StarNamer/dactyl-manuform-all/things/alps-holes.scad

union () {
  union () {
    union () {
      hull () {
        translate ([0, 0, 13]) {
          rotate (a=14.999999999999998, v=[0, 1, 0]) {
            translate ([0, 0, 0]) {
              translate ([0, 0, 0]) {
                translate ([0, 0, 239.07818057271746]) {
                  rotate (a=5.0, v=[0, 1, 0]) {
                    translate ([0, 0, -239.07818057271746]) {
                      translate ([0, 0, 85.26861330108649]) {
                        rotate (a=29.999999999999996, v=[1, 0, 0]) {
                          translate ([0, 0, -85.26861330108649]) {
                            translate ([-8.649999999999999, 8.649999999999999, 0]) {
                              translate ([0, 0, 2.25]) {
                                cube ([0.1, 0.1, 3.5], center=true);
                              }
                            }
                          }
                        }
                      }
                    }
                  }
                }
              }
            }
          }
        }
        translate ([0, 0, 13]) {
          rotate (a=14.999999999999998, v=[0, 1, 0]) {
            translate ([0, 0, 0]) {
              translate ([0, 0, 0]) {
                translate ([0, 0, 239.07818057271746]) {
                  rotate (a=10.0, v=[0, 1, 0]) {
                    translate ([0, 0, -239.07818057271746]) {
                      translate ([0, 0, 85.26861330108649]) {
                        rotate (a=29.999999999999996, v=[1, 0, 0]) {
                          translate ([0, 0, -85.26861330108649]) {
                            translate ([8.649999999999999, 8.649999999999999, 0]) {
                              translate ([0, 0, 2.25]) {
                                cube ([0.1, 0.1, 3.5], center=true);
                              }
                            }
                          }
                        }
                      }
                    }
                  }
                }
              }
            }
          }
        }
        translate ([0, 0, 13]) {
          rotate (a=14.999999999999998, v=[0, 1, 0]) {
            translate ([0, 0, 0]) {
              translate ([0, 0, 0]) {
                translate ([0, 0, 239.07818057271746]) {
                  rotate (a=5.0, v=[0, 1, 0]) {
                    translate ([0, 0, -239.07818057271746]) {
                      translate ([0, 0, 85.26861330108649]) {
                        rotate (a=29.999999999999996, v=[1, 0, 0]) {
                          translate ([0, 0, -85.26861330108649]) {
                            translate ([-8.649999999999999, -8.649999999999999, 0]) {
                              translate ([0, 0, 2.25]) {
                                cube ([0.1, 0.1, 3.5], center=true);
                              }
                            }
                          }
                        }
                      }
                    }
                  }
                }
              }
            }
          }
        }
      }
      hull () {
        translate ([0, 0, 13]) {
          rotate (a=14.999999999999998, v=[0, 1, 0]) {
            translate ([0, 0, 0]) {
              translate ([0, 0, 0]) {
                translate ([0, 0, 239.07818057271746]) {
                  rotate (a=10.0, v=[0, 1, 0]) {
                    translate ([0, 0, -239.07818057271746]) {
                      translate ([0, 0, 85.26861330108649]) {
                        rotate (a=29.999999999999996, v=[1, 0, 0]) {
                          translate ([0, 0, -85.26861330108649]) {
                            translate ([8.649999999999999, 8.649999999999999, 0]) {
                              translate ([0, 0, 2.25]) {
                                cube ([0.1, 0.1, 3.5], center=true);
                              }
                            }
                          }
                        }
                      }
                    }
                  }
                }
              }
            }
          }
        }
        translate ([0, 0, 13]) {
          rotate (a=14.999999999999998, v=[0, 1, 0]) {
            translate ([0, 0, 0]) {
              translate ([0, 0, 0]) {
                translate ([0, 0, 239.07818057271746]) {
                  rotate (a=5.0, v=[0, 1, 0]) {
                    translate ([0, 0, -239.07818057271746]) {
                      translate ([0, 0, 85.26861330108649]) {
                        rotate (a=29.999999999999996, v=[1, 0, 0]) {
                          translate ([0, 0, -85.26861330108649]) {
                            translate ([-8.649999999999999, -8.649999999999999, 0]) {
                              translate ([0, 0, 2.25]) {
                                cube ([0.1, 0.1, 3.5], center=true);
                              }
                            }
                          }
                        }
                      }
                    }
                  }
                }
              }
            }
          }
        }
        translate ([0, 0, 13]) {
          rotate (a=14.999999999999998, v=[0, 1, 0]) {
            translate ([0, 0, 0]) {
              translate ([0, 0, 0]) {
                translate ([0, 0, 239.07818057271746]) {
                  rotate (a=10.0, v=[0, 1, 0]) {
                    translate ([0, 0, -239.07818057271746]) {
                      translate ([0, 0, 85.26861330108649]) {
                        rotate (a=29.999999999999996, v=[1, 0, 0]) {
                          translate ([0, 0, -85.26861330108649]) {
                            translate ([8.649999999999999, -8.649999999999999, 0]) {
                              translate ([0, 0, 2.25]) {
                                cube ([0.1, 0.1, 3.5], center=true);
                              }
                            }
                          }
                        }
                      }
                    }
                  }
                }
              }
            }
          }
        }
      }
    }
    union () {
      hull () {
        translate ([0, 0, 13]) {
          rotate (a=14.999999999999998, v=[0, 1, 0]) {
            translate ([7.2, 0, 0]) {
              translate ([0, 0, 0]) {
                translate ([0, 0, 239.07818057271746]) {
                  rotate (a=5.0, v=[0, 1, 0]) {
                    translate ([0, 0, -239.07818057271746]) {
                      translate ([0, 0, 85.26861330108649]) {
                        rotate (a=14.999999999999998, v=[1, 0, 0]) {
                          translate ([0, 0, -85.26861330108649]) {
                            translate ([-8.649999999999999, 8.649999999999999, 0]) {
                              translate ([0, 0, 2.25]) {
                                cube ([0.1, 0.1, 3.5], center=true);
                              }
                            }
                          }
                        }
                      }
                    }
                  }
                }
              }
            }
          }
        }
        translate ([0, 0, 13]) {
          rotate (a=14.999999999999998, v=[0, 1, 0]) {
            translate ([7.2, 0, 0]) {
              translate ([0, 0, 0]) {
                translate ([0, 0, 239.07818057271746]) {
                  rotate (a=10.0, v=[0, 1, 0]) {
                    translate ([0, 0, -239.07818057271746]) {
                      translate ([0, 0, 85.26861330108649]) {
                        rotate (a=14.999999999999998, v=[1, 0, 0]) {
                          translate ([0, 0, -85.26861330108649]) {
                            translate ([8.649999999999999, 8.649999999999999, 0]) {
                              translate ([0, 0, 2.25]) {
                                cube ([0.1, 0.1, 3.5], center=true);
                              }
                            }
                          }
                        }
                      }
                    }
                  }
                }
              }
            }
          }
        }
        translate ([0, 0, 13]) {
          rotate (a=14.999999999999998, v=[0, 1, 0]) {
            translate ([7.2, 0, 0]) {
              translate ([0, 0, 0]) {
                translate ([0, 0, 239.07818057271746]) {
                  rotate (a=5.0, v=[0, 1, 0]) {
                    translate ([0, 0, -239.07818057271746]) {
                      translate ([0, 0, 85.26861330108649]) {
                        rotate (a=14.999999999999998, v=[1, 0, 0]) {
                          translate ([0, 0, -85.26861330108649]) {
                            translate ([-8.649999999999999, -8.649999999999999, 0]) {
                              translate ([0, 0, 2.25]) {
                                cube ([0.1, 0.1, 3.5], center=true);
                              }
                            }
                          }
                        }
                      }
                    }
                  }
                }
              }
            }
          }
        }
      }
      hull () {
        translate ([0, 0, 13]) {
          rotate (a=14.999999999999998, v=[0, 1, 0]) {
            translate ([7.2, 0, 0]) {
              translate ([0, 0, 0]) {
                translate ([0, 0, 239.07818057271746]) {
                  rotate (a=10.0, v=[0, 1, 0]) {
                    translate ([0, 0, -239.07818057271746]) {
                      translate ([0, 0, 85.26861330108649]) {
                        rotate (a=14.999999999999998, v=[1, 0, 0]) {
                          translate ([0, 0, -85.26861330108649]) {
                            translate ([8.649999999999999, 8.649999999999999, 0]) {
                              translate ([0, 0, 2.25]) {
                                cube ([0.1, 0.1, 3.5], center=true);
                              }
                            }
                          }
                        }
                      }
                    }
                  }
                }
              }
            }
          }
        }
        translate ([0, 0, 13]) {
          rotate (a=14.999999999999998, v=[0, 1, 0]) {
            translate ([7.2, 0, 0]) {
              translate ([0, 0, 0]) {
                translate ([0, 0, 239.07818057271746]) {
                  rotate (a=5.0, v=[0, 1, 0]) {
                    translate ([0, 0, -239.07818057271746]) {
                      translate ([0, 0, 85.26861330108649]) {
                        rotate (a=14.999999999999998, v=[1, 0, 0]) {
                          translate ([0, 0, -85.26861330108649]) {
                            translate ([-8.649999999999999, -8.649999999999999, 0]) {
                              translate ([0, 0, 2.25]) {
                                cube ([0.1, 0.1, 3.5], center=true);
                              }
                            }
                          }
                        }
                      }
                    }
                  }
                }
              }
            }
          }
        }
        translate ([0, 0, 13]) {
          rotate (a=14.999999999999998, v=[0, 1, 0]) {
            translate ([7.2, 0, 0]) {
              translate ([0, 0, 0]) {
                translate ([0, 0, 239.07818057271746]) {
                  rotate (a=10.0, v=[0, 1, 0]) {
                    translate ([0, 0, -239.07818057271746]) {
                      translate ([0, 0, 85.26861330108649]) {
                        rotate (a=14.999999999999998, v=[1, 0, 0]) {
                          translate ([0, 0, -85.26861330108649]) {
                            translate ([8.649999999999999, -8.649999999999999, 0]) {
                              translate ([0, 0, 2.25]) {
                                cube ([0.1, 0.1, 3.5], center=true);
                              }
                            }
                          }
                        }
                      }
                    }
                  }
                }
              }
            }
          }
        }
      }
    }
    union () {
      hull () {
        translate ([0, 0, 13]) {
          rotate (a=14.999999999999998, v=[0, 1, 0]) {
            translate ([14.4, 0, 0]) {
              translate ([0, 0, 0]) {
                translate ([0, 0, 239.07818057271746]) {
                  rotate (a=5.0, v=[0, 1, 0]) {
                    translate ([0, 0, -239.07818057271746]) {
                      translate ([0, 0, 85.26861330108649]) {
                        rotate (a=0.0, v=[1, 0, 0]) {
                          translate ([0, 0, -85.26861330108649]) {
                            translate ([-8.649999999999999, 8.649999999999999, 0]) {
                              translate ([0, 0, 2.25]) {
                                cube ([0.1, 0.1, 3.5], center=true);
                              }
                            }
                          }
                        }
                      }
                    }
                  }
                }
              }
            }
          }
        }
        translate ([0, 0, 13]) {
          rotate (a=14.999999999999998, v=[0, 1, 0]) {
            translate ([14.4, 0, 0]) {
              translate ([0, 0, 0]) {
                translate ([0, 0, 239.07818057271746]) {
                  rotate (a=10.0, v=[0, 1, 0]) {
                    translate ([0, 0, -239.07818057271746]) {
                      translate ([0, 0, 85.26861330108649]) {
                        rotate (a=0.0, v=[1, 0, 0]) {
                          translate ([0, 0, -85.26861330108649]) {
                            translate ([8.649999999999999, 8.649999999999999, 0]) {
                              translate ([0, 0, 2.25]) {
                                cube ([0.1, 0.1, 3.5], center=true);
                              }
                            }
                          }
                        }
                      }
                    }
                  }
                }
              }
            }
          }
        }
        translate ([0, 0, 13]) {
          rotate (a=14.999999999999998, v=[0, 1, 0]) {
            translate ([14.4, 0, 0]) {
              translate ([0, 0, 0]) {
                translate ([0, 0, 239.07818057271746]) {
                  rotate (a=5.0, v=[0, 1, 0]) {
                    translate ([0, 0, -239.07818057271746]) {
                      translate ([0, 0, 85.26861330108649]) {
                        rotate (a=0.0, v=[1, 0, 0]) {
                          translate ([0, 0, -85.26861330108649]) {
                            translate ([-8.649999999999999, -8.649999999999999, 0]) {
                              translate ([0, 0, 2.25]) {
                                cube ([0.1, 0.1, 3.5], center=true);
                              }
                            }
                          }
                        }
                      }
                    }
                  }
                }
              }
            }
          }
        }
      }
      hull () {
        translate ([0, 0, 13]) {
          rotate (a=14.999999999999998, v=[0, 1, 0]) {
            translate ([14.4, 0, 0]) {
              translate ([0, 0, 0]) {
                translate ([0, 0, 239.07818057271746]) {
                  rotate (a=10.0, v=[0, 1, 0]) {
                    translate ([0, 0, -239.07818057271746]) {
                      translate ([0, 0, 85.26861330108649]) {
                        rotate (a=0.0, v=[1, 0, 0]) {
                          translate ([0, 0, -85.26861330108649]) {
                            translate ([8.649999999999999, 8.649999999999999, 0]) {
                              translate ([0, 0, 2.25]) {
                                cube ([0.1, 0.1, 3.5], center=true);
                              }
                            }
                          }
                        }
                      }
                    }
                  }
                }
              }
            }
          }
        }
        translate ([0, 0, 13]) {
          rotate (a=14.999999999999998, v=[0, 1, 0]) {
            translate ([14.4, 0, 0]) {
              translate ([0, 0, 0]) {
                translate ([0, 0, 239.07818057271746]) {
                  rotate (a=5.0, v=[0, 1, 0]) {
                    translate ([0, 0, -239.07818057271746]) {
                      translate ([0, 0, 85.26861330108649]) {
                        rotate (a=0.0, v=[1, 0, 0]) {
                          translate ([0, 0, -85.26861330108649]) {
                            translate ([-8.649999999999999, -8.649999999999999, 0]) {
                              translate ([0, 0, 2.25]) {
                                cube ([0.1, 0.1, 3.5], center=true);
                              }
                            }
                          }
                        }
                      }
                    }
                  }
                }
              }
            }
          }
        }
        translate ([0, 0, 13]) {
          rotate (a=14.999999999999998, v=[0, 1, 0]) {
            translate ([14.4, 0, 0]) {
              translate ([0, 0, 0]) {
                translate ([0, 0, 239.07818057271746]) {
                  rotate (a=10.0, v=[0, 1, 0]) {
                    translate ([0, 0, -239.07818057271746]) {
                      translate ([0, 0, 85.26861330108649]) {
                        rotate (a=0.0, v=[1, 0, 0]) {
                          translate ([0, 0, -85.26861330108649]) {
                            translate ([8.649999999999999, -8.649999999999999, 0]) {
                              translate ([0, 0, 2.25]) {
                                cube ([0.1, 0.1, 3.5], center=true);
                              }
                            }
                          }
                        }
                      }
                    }
                  }
                }
              }
            }
          }
        }
      }
    }
    union () {
      hull () {
        translate ([0, 0, 13]) {
          rotate (a=14.999999999999998, v=[0, 1, 0]) {
            translate ([21.6, 0, 0]) {
              translate ([0, 0, 0]) {
                translate ([0, 0, 239.07818057271746]) {
                  rotate (a=5.0, v=[0, 1, 0]) {
                    translate ([0, 0, -239.07818057271746]) {
                      translate ([0, 0, 85.26861330108649]) {
                        rotate (a=-14.999999999999998, v=[1, 0, 0]) {
                          translate ([0, 0, -85.26861330108649]) {
                            translate ([-8.649999999999999, 8.649999999999999, 0]) {
                              translate ([0, 0, 2.25]) {
                                cube ([0.1, 0.1, 3.5], center=true);
                              }
                            }
                          }
                        }
                      }
                    }
                  }
                }
              }
            }
          }
        }
        translate ([0, 0, 13]) {
          rotate (a=14.999999999999998, v=[0, 1, 0]) {
            translate ([21.6, 0, 0]) {
              translate ([0, 0, 0]) {
                translate ([0, 0, 239.07818057271746]) {
                  rotate (a=10.0, v=[0, 1, 0]) {
                    translate ([0, 0, -239.07818057271746]) {
                      translate ([0, 0, 85.26861330108649]) {
                        rotate (a=-14.999999999999998, v=[1, 0, 0]) {
                          translate ([0, 0, -85.26861330108649]) {
                            translate ([8.649999999999999, 8.649999999999999, 0]) {
                              translate ([0, 0, 2.25]) {
                                cube ([0.1, 0.1, 3.5], center=true);
                              }
                            }
                          }
                        }
                      }
                    }
                  }
                }
              }
            }
          }
        }
        translate ([0, 0, 13]) {
          rotate (a=14.999999999999998, v=[0, 1, 0]) {
            translate ([21.6, 0, 0]) {
              translate ([0, 0, 0]) {
                translate ([0, 0, 239.07818057271746]) {
                  rotate (a=5.0, v=[0, 1, 0]) {
                    translate ([0, 0, -239.07818057271746]) {
                      translate ([0, 0, 85.26861330108649]) {
                        rotate (a=-14.999999999999998, v=[1, 0, 0]) {
                          translate ([0, 0, -85.26861330108649]) {
                            translate ([-8.649999999999999, -8.649999999999999, 0]) {
                              translate ([0, 0, 2.25]) {
                                cube ([0.1, 0.1, 3.5], center=true);
                              }
                            }
                          }
                        }
                      }
                    }
                  }
                }
              }
            }
          }
        }
      }
      hull () {
        translate ([0, 0, 13]) {
          rotate (a=14.999999999999998, v=[0, 1, 0]) {
            translate ([21.6, 0, 0]) {
              translate ([0, 0, 0]) {
                translate ([0, 0, 239.07818057271746]) {
                  rotate (a=10.0, v=[0, 1, 0]) {
                    translate ([0, 0, -239.07818057271746]) {
                      translate ([0, 0, 85.26861330108649]) {
                        rotate (a=-14.999999999999998, v=[1, 0, 0]) {
                          translate ([0, 0, -85.26861330108649]) {
                            translate ([8.649999999999999, 8.649999999999999, 0]) {
                              translate ([0, 0, 2.25]) {
                                cube ([0.1, 0.1, 3.5], center=true);
                              }
                            }
                          }
                        }
                      }
                    }
                  }
                }
              }
            }
          }
        }
        translate ([0, 0, 13]) {
          rotate (a=14.999999999999998, v=[0, 1, 0]) {
            translate ([21.6, 0, 0]) {
              translate ([0, 0, 0]) {
                translate ([0, 0, 239.07818057271746]) {
                  rotate (a=5.0, v=[0, 1, 0]) {
                    translate ([0, 0, -239.07818057271746]) {
                      translate ([0, 0, 85.26861330108649]) {
                        rotate (a=-14.999999999999998, v=[1, 0, 0]) {
                          translate ([0, 0, -85.26861330108649]) {
                            translate ([-8.649999999999999, -8.649999999999999, 0]) {
                              translate ([0, 0, 2.25]) {
                                cube ([0.1, 0.1, 3.5], center=true);
                              }
                            }
                          }
                        }
                      }
                    }
                  }
                }
              }
            }
          }
        }
        translate ([0, 0, 13]) {
          rotate (a=14.999999999999998, v=[0, 1, 0]) {
            translate ([21.6, 0, 0]) {
              translate ([0, 0, 0]) {
                translate ([0, 0, 239.07818057271746]) {
                  rotate (a=10.0, v=[0, 1, 0]) {
                    translate ([0, 0, -239.07818057271746]) {
                      translate ([0, 0, 85.26861330108649]) {
                        rotate (a=-14.999999999999998, v=[1, 0, 0]) {
                          translate ([0, 0, -85.26861330108649]) {
                            translate ([8.649999999999999, -8.649999999999999, 0]) {
                              translate ([0, 0, 2.25]) {
                                cube ([0.1, 0.1, 3.5], center=true);
                              }
                            }
                          }
                        }
                      }
                    }
                  }
                }
              }
            }
          }
        }
      }
    }
    union () {
      hull () {
        translate ([0, 0, 13]) {
          rotate (a=14.999999999999998, v=[0, 1, 0]) {
            translate ([0, 0, 0]) {
              translate ([0, 2.82, -3.0]) {
                translate ([0, 0, 239.07818057271746]) {
                  rotate (a=0.0, v=[0, 1, 0]) {
                    translate ([0, 0, -239.07818057271746]) {
                      translate ([0, 0, 85.26861330108649]) {
                        rotate (a=29.999999999999996, v=[1, 0, 0]) {
                          translate ([0, 0, -85.26861330108649]) {
                            translate ([-8.649999999999999, 8.649999999999999, 0]) {
                              translate ([0, 0, 2.25]) {
                                cube ([0.1, 0.1, 3.5], center=true);
                              }
                            }
                          }
                        }
                      }
                    }
                  }
                }
              }
            }
          }
        }
        translate ([0, 0, 13]) {
          rotate (a=14.999999999999998, v=[0, 1, 0]) {
            translate ([0, 0, 0]) {
              translate ([0, 0, 0]) {
                translate ([0, 0, 239.07818057271746]) {
                  rotate (a=5.0, v=[0, 1, 0]) {
                    translate ([0, 0, -239.07818057271746]) {
                      translate ([0, 0, 85.26861330108649]) {
                        rotate (a=29.999999999999996, v=[1, 0, 0]) {
                          translate ([0, 0, -85.26861330108649]) {
                            translate ([8.649999999999999, 8.649999999999999, 0]) {
                              translate ([0, 0, 2.25]) {
                                cube ([0.1, 0.1, 3.5], center=true);
                              }
                            }
                          }
                        }
                      }
                    }
                  }
                }
              }
            }
          }
        }
        translate ([0, 0, 13]) {
          rotate (a=14.999999999999998, v=[0, 1, 0]) {
            translate ([0, 0, 0]) {
              translate ([0, 2.82, -3.0]) {
                translate ([0, 0, 239.07818057271746]) {
                  rotate (a=0.0, v=[0, 1, 0]) {
                    translate ([0, 0, -239.07818057271746]) {
                      translate ([0, 0, 85.26861330108649]) {
                        rotate (a=29.999999999999996, v=[1, 0, 0]) {
                          translate ([0, 0, -85.26861330108649]) {
                            translate ([-8.649999999999999, -8.649999999999999, 0]) {
                              translate ([0, 0, 2.25]) {
                                cube ([0.1, 0.1, 3.5], center=true);
                              }
                            }
                          }
                        }
                      }
                    }
                  }
                }
              }
            }
          }
        }
      }
      hull () {
        translate ([0, 0, 13]) {
          rotate (a=14.999999999999998, v=[0, 1, 0]) {
            translate ([0, 0, 0]) {
              translate ([0, 0, 0]) {
                translate ([0, 0, 239.07818057271746]) {
                  rotate (a=5.0, v=[0, 1, 0]) {
                    translate ([0, 0, -239.07818057271746]) {
                      translate ([0, 0, 85.26861330108649]) {
                        rotate (a=29.999999999999996, v=[1, 0, 0]) {
                          translate ([0, 0, -85.26861330108649]) {
                            translate ([8.649999999999999, 8.649999999999999, 0]) {
                              translate ([0, 0, 2.25]) {
                                cube ([0.1, 0.1, 3.5], center=true);
                              }
                            }
                          }
                        }
                      }
                    }
                  }
                }
              }
            }
          }
        }
        translate ([0, 0, 13]) {
          rotate (a=14.999999999999998, v=[0, 1, 0]) {
            translate ([0, 0, 0]) {
              translate ([0, 2.82, -3.0]) {
                translate ([0, 0, 239.07818057271746]) {
                  rotate (a=0.0, v=[0, 1, 0]) {
                    translate ([0, 0, -239.07818057271746]) {
                      translate ([0, 0, 85.26861330108649]) {
                        rotate (a=29.999999999999996, v=[1, 0, 0]) {
                          translate ([0, 0, -85.26861330108649]) {
                            translate ([-8.649999999999999, -8.649999999999999, 0]) {
                              translate ([0, 0, 2.25]) {
                                cube ([0.1, 0.1, 3.5], center=true);
                              }
                            }
                          }
                        }
                      }
                    }
                  }
                }
              }
            }
          }
        }
        translate ([0, 0, 13]) {
          rotate (a=14.999999999999998, v=[0, 1, 0]) {
            translate ([0, 0, 0]) {
              translate ([0, 0, 0]) {
                translate ([0, 0, 239.07818057271746]) {
                  rotate (a=5.0, v=[0, 1, 0]) {
                    translate ([0, 0, -239.07818057271746]) {
                      translate ([0, 0, 85.26861330108649]) {
                        rotate (a=29.999999999999996, v=[1, 0, 0]) {
                          translate ([0, 0, -85.26861330108649]) {
                            translate ([8.649999999999999, -8.649999999999999, 0]) {
                              translate ([0, 0, 2.25]) {
                                cube ([0.1, 0.1, 3.5], center=true);
                              }
                            }
                          }
                        }
                      }
                    }
                  }
                }
              }
            }
          }
        }
      }
    }
    union () {
      hull () {
        translate ([0, 0, 13]) {
          rotate (a=14.999999999999998, v=[0, 1, 0]) {
            translate ([7.2, 0, 0]) {
              translate ([0, 2.82, -3.0]) {
                translate ([0, 0, 239.07818057271746]) {
                  rotate (a=0.0, v=[0, 1, 0]) {
                    translate ([0, 0, -239.07818057271746]) {
                      translate ([0, 0, 85.26861330108649]) {
                        rotate (a=14.999999999999998, v=[1, 0, 0]) {
                          translate ([0, 0, -85.26861330108649]) {
                            translate ([-8.649999999999999, 8.649999999999999, 0]) {
                              translate ([0, 0, 2.25]) {
                                cube ([0.1, 0.1, 3.5], center=true);
                              }
                            }
                          }
                        }
                      }
                    }
                  }
                }
              }
            }
          }
        }
        translate ([0, 0, 13]) {
          rotate (a=14.999999999999998, v=[0, 1, 0]) {
            translate ([7.2, 0, 0]) {
              translate ([0, 0, 0]) {
                translate ([0, 0, 239.07818057271746]) {
                  rotate (a=5.0, v=[0, 1, 0]) {
                    translate ([0, 0, -239.07818057271746]) {
                      translate ([0, 0, 85.26861330108649]) {
                        rotate (a=14.999999999999998, v=[1, 0, 0]) {
                          translate ([0, 0, -85.26861330108649]) {
                            translate ([8.649999999999999, 8.649999999999999, 0]) {
                              translate ([0, 0, 2.25]) {
                                cube ([0.1, 0.1, 3.5], center=true);
                              }
                            }
                          }
                        }
                      }
                    }
                  }
                }
              }
            }
          }
        }
        translate ([0, 0, 13]) {
          rotate (a=14.999999999999998, v=[0, 1, 0]) {
            translate ([7.2, 0, 0]) {
              translate ([0, 2.82, -3.0]) {
                translate ([0, 0, 239.07818057271746]) {
                  rotate (a=0.0, v=[0, 1, 0]) {
                    translate ([0, 0, -239.07818057271746]) {
                      translate ([0, 0, 85.26861330108649]) {
                        rotate (a=14.999999999999998, v=[1, 0, 0]) {
                          translate ([0, 0, -85.26861330108649]) {
                            translate ([-8.649999999999999, -8.649999999999999, 0]) {
                              translate ([0, 0, 2.25]) {
                                cube ([0.1, 0.1, 3.5], center=true);
                              }
                            }
                          }
                        }
                      }
                    }
                  }
                }
              }
            }
          }
        }
      }
      hull () {
        translate ([0, 0, 13]) {
          rotate (a=14.999999999999998, v=[0, 1, 0]) {
            translate ([7.2, 0, 0]) {
              translate ([0, 0, 0]) {
                translate ([0, 0, 239.07818057271746]) {
                  rotate (a=5.0, v=[0, 1, 0]) {
                    translate ([0, 0, -239.07818057271746]) {
                      translate ([0, 0, 85.26861330108649]) {
                        rotate (a=14.999999999999998, v=[1, 0, 0]) {
                          translate ([0, 0, -85.26861330108649]) {
                            translate ([8.649999999999999, 8.649999999999999, 0]) {
                              translate ([0, 0, 2.25]) {
                                cube ([0.1, 0.1, 3.5], center=true);
                              }
                            }
                          }
                        }
                      }
                    }
                  }
                }
              }
            }
          }
        }
        translate ([0, 0, 13]) {
          rotate (a=14.999999999999998, v=[0, 1, 0]) {
            translate ([7.2, 0, 0]) {
              translate ([0, 2.82, -3.0]) {
                translate ([0, 0, 239.07818057271746]) {
                  rotate (a=0.0, v=[0, 1, 0]) {
                    translate ([0, 0, -239.07818057271746]) {
                      translate ([0, 0, 85.26861330108649]) {
                        rotate (a=14.999999999999998, v=[1, 0, 0]) {
                          translate ([0, 0, -85.26861330108649]) {
                            translate ([-8.649999999999999, -8.649999999999999, 0]) {
                              translate ([0, 0, 2.25]) {
                                cube ([0.1, 0.1, 3.5], center=true);
                              }
                            }
                          }
                        }
                      }
                    }
                  }
                }
              }
            }
          }
        }
        translate ([0, 0, 13]) {
          rotate (a=14.999999999999998, v=[0, 1, 0]) {
            translate ([7.2, 0, 0]) {
              translate ([0, 0, 0]) {
                translate ([0, 0, 239.07818057271746]) {
                  rotate (a=5.0, v=[0, 1, 0]) {
                    translate ([0, 0, -239.07818057271746]) {
                      translate ([0, 0, 85.26861330108649]) {
                        rotate (a=14.999999999999998, v=[1, 0, 0]) {
                          translate ([0, 0, -85.26861330108649]) {
                            translate ([8.649999999999999, -8.649999999999999, 0]) {
                              translate ([0, 0, 2.25]) {
                                cube ([0.1, 0.1, 3.5], center=true);
                              }
                            }
                          }
                        }
                      }
                    }
                  }
                }
              }
            }
          }
        }
      }
    }
    union () {
      hull () {
        translate ([0, 0, 13]) {
          rotate (a=14.999999999999998, v=[0, 1, 0]) {
            translate ([14.4, 0, 0]) {
              translate ([0, 2.82, -3.0]) {
                translate ([0, 0, 239.07818057271746]) {
                  rotate (a=0.0, v=[0, 1, 0]) {
                    translate ([0, 0, -239.07818057271746]) {
                      translate ([0, 0, 85.26861330108649]) {
                        rotate (a=0.0, v=[1, 0, 0]) {
                          translate ([0, 0, -85.26861330108649]) {
                            translate ([-8.649999999999999, 8.649999999999999, 0]) {
                              translate ([0, 0, 2.25]) {
                                cube ([0.1, 0.1, 3.5], center=true);
                              }
                            }
                          }
                        }
                      }
                    }
                  }
                }
              }
            }
          }
        }
        translate ([0, 0, 13]) {
          rotate (a=14.999999999999998, v=[0, 1, 0]) {
            translate ([14.4, 0, 0]) {
              translate ([0, 0, 0]) {
                translate ([0, 0, 239.07818057271746]) {
                  rotate (a=5.0, v=[0, 1, 0]) {
                    translate ([0, 0, -239.07818057271746]) {
                      translate ([0, 0, 85.26861330108649]) {
                        rotate (a=0.0, v=[1, 0, 0]) {
                          translate ([0, 0, -85.26861330108649]) {
                            translate ([8.649999999999999, 8.649999999999999, 0]) {
                              translate ([0, 0, 2.25]) {
                                cube ([0.1, 0.1, 3.5], center=true);
                              }
                            }
                          }
                        }
                      }
                    }
                  }
                }
              }
            }
          }
        }
        translate ([0, 0, 13]) {
          rotate (a=14.999999999999998, v=[0, 1, 0]) {
            translate ([14.4, 0, 0]) {
              translate ([0, 2.82, -3.0]) {
                translate ([0, 0, 239.07818057271746]) {
                  rotate (a=0.0, v=[0, 1, 0]) {
                    translate ([0, 0, -239.07818057271746]) {
                      translate ([0, 0, 85.26861330108649]) {
                        rotate (a=0.0, v=[1, 0, 0]) {
                          translate ([0, 0, -85.26861330108649]) {
                            translate ([-8.649999999999999, -8.649999999999999, 0]) {
                              translate ([0, 0, 2.25]) {
                                cube ([0.1, 0.1, 3.5], center=true);
                              }
                            }
                          }
                        }
                      }
                    }
                  }
                }
              }
            }
          }
        }
      }
      hull () {
        translate ([0, 0, 13]) {
          rotate (a=14.999999999999998, v=[0, 1, 0]) {
            translate ([14.4, 0, 0]) {
              translate ([0, 0, 0]) {
                translate ([0, 0, 239.07818057271746]) {
                  rotate (a=5.0, v=[0, 1, 0]) {
                    translate ([0, 0, -239.07818057271746]) {
                      translate ([0, 0, 85.26861330108649]) {
                        rotate (a=0.0, v=[1, 0, 0]) {
                          translate ([0, 0, -85.26861330108649]) {
                            translate ([8.649999999999999, 8.649999999999999, 0]) {
                              translate ([0, 0, 2.25]) {
                                cube ([0.1, 0.1, 3.5], center=true);
                              }
                            }
                          }
                        }
                      }
                    }
                  }
                }
              }
            }
          }
        }
        translate ([0, 0, 13]) {
          rotate (a=14.999999999999998, v=[0, 1, 0]) {
            translate ([14.4, 0, 0]) {
              translate ([0, 2.82, -3.0]) {
                translate ([0, 0, 239.07818057271746]) {
                  rotate (a=0.0, v=[0, 1, 0]) {
                    translate ([0, 0, -239.07818057271746]) {
                      translate ([0, 0, 85.26861330108649]) {
                        rotate (a=0.0, v=[1, 0, 0]) {
                          translate ([0, 0, -85.26861330108649]) {
                            translate ([-8.649999999999999, -8.649999999999999, 0]) {
                              translate ([0, 0, 2.25]) {
                                cube ([0.1, 0.1, 3.5], center=true);
                              }
                            }
                          }
                        }
                      }
                    }
                  }
                }
              }
            }
          }
        }
        translate ([0, 0, 13]) {
          rotate (a=14.999999999999998, v=[0, 1, 0]) {
            translate ([14.4, 0, 0]) {
              translate ([0, 0, 0]) {
                translate ([0, 0, 239.07818057271746]) {
                  rotate (a=5.0, v=[0, 1, 0]) {
                    translate ([0, 0, -239.07818057271746]) {
                      translate ([0, 0, 85.26861330108649]) {
                        rotate (a=0.0, v=[1, 0, 0]) {
                          translate ([0, 0, -85.26861330108649]) {
                            translate ([8.649999999999999, -8.649999999999999, 0]) {
                              translate ([0, 0, 2.25]) {
                                cube ([0.1, 0.1, 3.5], center=true);
                              }
                            }
                          }
                        }
                      }
                    }
                  }
                }
              }
            }
          }
        }
      }
    }
    union () {
      hull () {
        translate ([0, 0, 13]) {
          rotate (a=14.999999999999998, v=[0, 1, 0]) {
            translate ([21.6, 0, 0]) {
              translate ([0, 2.82, -3.0]) {
                translate ([0, 0, 239.07818057271746]) {
                  rotate (a=0.0, v=[0, 1, 0]) {
                    translate ([0, 0, -239.07818057271746]) {
                      translate ([0, 0, 85.26861330108649]) {
                        rotate (a=-14.999999999999998, v=[1, 0, 0]) {
                          translate ([0, 0, -85.26861330108649]) {
                            translate ([-8.649999999999999, 8.649999999999999, 0]) {
                              translate ([0, 0, 2.25]) {
                                cube ([0.1, 0.1, 3.5], center=true);
                              }
                            }
                          }
                        }
                      }
                    }
                  }
                }
              }
            }
          }
        }
        translate ([0, 0, 13]) {
          rotate (a=14.999999999999998, v=[0, 1, 0]) {
            translate ([21.6, 0, 0]) {
              translate ([0, 0, 0]) {
                translate ([0, 0, 239.07818057271746]) {
                  rotate (a=5.0, v=[0, 1, 0]) {
                    translate ([0, 0, -239.07818057271746]) {
                      translate ([0, 0, 85.26861330108649]) {
                        rotate (a=-14.999999999999998, v=[1, 0, 0]) {
                          translate ([0, 0, -85.26861330108649]) {
                            translate ([8.649999999999999, 8.649999999999999, 0]) {
                              translate ([0, 0, 2.25]) {
                                cube ([0.1, 0.1, 3.5], center=true);
                              }
                            }
                          }
                        }
                      }
                    }
                  }
                }
              }
            }
          }
        }
        translate ([0, 0, 13]) {
          rotate (a=14.999999999999998, v=[0, 1, 0]) {
            translate ([21.6, 0, 0]) {
              translate ([0, 2.82, -3.0]) {
                translate ([0, 0, 239.07818057271746]) {
                  rotate (a=0.0, v=[0, 1, 0]) {
                    translate ([0, 0, -239.07818057271746]) {
                      translate ([0, 0, 85.26861330108649]) {
                        rotate (a=-14.999999999999998, v=[1, 0, 0]) {
                          translate ([0, 0, -85.26861330108649]) {
                            translate ([-8.649999999999999, -8.649999999999999, 0]) {
                              translate ([0, 0, 2.25]) {
                                cube ([0.1, 0.1, 3.5], center=true);
                              }
                            }
                          }
                        }
                      }
                    }
                  }
                }
              }
            }
          }
        }
      }
      hull () {
        translate ([0, 0, 13]) {
          rotate (a=14.999999999999998, v=[0, 1, 0]) {
            translate ([21.6, 0, 0]) {
              translate ([0, 0, 0]) {
                translate ([0, 0, 239.07818057271746]) {
                  rotate (a=5.0, v=[0, 1, 0]) {
                    translate ([0, 0, -239.07818057271746]) {
                      translate ([0, 0, 85.26861330108649]) {
                        rotate (a=-14.999999999999998, v=[1, 0, 0]) {
                          translate ([0, 0, -85.26861330108649]) {
                            translate ([8.649999999999999, 8.649999999999999, 0]) {
                              translate ([0, 0, 2.25]) {
                                cube ([0.1, 0.1, 3.5], center=true);
                              }
                            }
                          }
                        }
                      }
                    }
                  }
                }
              }
            }
          }
        }
        translate ([0, 0, 13]) {
          rotate (a=14.999999999999998, v=[0, 1, 0]) {
            translate ([21.6, 0, 0]) {
              translate ([0, 2.82, -3.0]) {
                translate ([0, 0, 239.07818057271746]) {
                  rotate (a=0.0, v=[0, 1, 0]) {
                    translate ([0, 0, -239.07818057271746]) {
                      translate ([0, 0, 85.26861330108649]) {
                        rotate (a=-14.999999999999998, v=[1, 0, 0]) {
                          translate ([0, 0, -85.26861330108649]) {
                            translate ([-8.649999999999999, -8.649999999999999, 0]) {
                              translate ([0, 0, 2.25]) {
                                cube ([0.1, 0.1, 3.5], center=true);
                              }
                            }
                          }
                        }
                      }
                    }
                  }
                }
              }
            }
          }
        }
        translate ([0, 0, 13]) {
          rotate (a=14.999999999999998, v=[0, 1, 0]) {
            translate ([21.6, 0, 0]) {
              translate ([0, 0, 0]) {
                translate ([0, 0, 239.07818057271746]) {
                  rotate (a=5.0, v=[0, 1, 0]) {
                    translate ([0, 0, -239.07818057271746]) {
                      translate ([0, 0, 85.26861330108649]) {
                        rotate (a=-14.999999999999998, v=[1, 0, 0]) {
                          translate ([0, 0, -85.26861330108649]) {
                            translate ([8.649999999999999, -8.649999999999999, 0]) {
                              translate ([0, 0, 2.25]) {
                                cube ([0.1, 0.1, 3.5], center=true);
                              }
                            }
                          }
                        }
                      }
                    }
                  }
                }
              }
            }
          }
        }
      }
    }
    union () {
      hull () {
        translate ([0, 0, 13]) {
          rotate (a=14.999999999999998, v=[0, 1, 0]) {
            translate ([28.8, 0, 0]) {
              translate ([0, 2.82, -3.0]) {
                translate ([0, 0, 239.07818057271746]) {
                  rotate (a=0.0, v=[0, 1, 0]) {
                    translate ([0, 0, -239.07818057271746]) {
                      translate ([0, 0, 85.26861330108649]) {
                        rotate (a=-29.999999999999996, v=[1, 0, 0]) {
                          translate ([0, 0, -85.26861330108649]) {
                            translate ([-8.649999999999999, 8.649999999999999, 0]) {
                              translate ([0, 0, 2.25]) {
                                cube ([0.1, 0.1, 3.5], center=true);
                              }
                            }
                          }
                        }
                      }
                    }
                  }
                }
              }
            }
          }
        }
        translate ([0, 0, 13]) {
          rotate (a=14.999999999999998, v=[0, 1, 0]) {
            translate ([28.8, 0, 0]) {
              translate ([0, 0, 0]) {
                translate ([0, 0, 239.07818057271746]) {
                  rotate (a=5.0, v=[0, 1, 0]) {
                    translate ([0, 0, -239.07818057271746]) {
                      translate ([0, 0, 85.26861330108649]) {
                        rotate (a=-29.999999999999996, v=[1, 0, 0]) {
                          translate ([0, 0, -85.26861330108649]) {
                            translate ([8.649999999999999, 8.649999999999999, 0]) {
                              translate ([0, 0, 2.25]) {
                                cube ([0.1, 0.1, 3.5], center=true);
                              }
                            }
                          }
                        }
                      }
                    }
                  }
                }
              }
            }
          }
        }
        translate ([0, 0, 13]) {
          rotate (a=14.999999999999998, v=[0, 1, 0]) {
            translate ([28.8, 0, 0]) {
              translate ([0, 2.82, -3.0]) {
                translate ([0, 0, 239.07818057271746]) {
                  rotate (a=0.0, v=[0, 1, 0]) {
                    translate ([0, 0, -239.07818057271746]) {
                      translate ([0, 0, 85.26861330108649]) {
                        rotate (a=-29.999999999999996, v=[1, 0, 0]) {
                          translate ([0, 0, -85.26861330108649]) {
                            translate ([-8.649999999999999, -8.649999999999999, 0]) {
                              translate ([0, 0, 2.25]) {
                                cube ([0.1, 0.1, 3.5], center=true);
                              }
                            }
                          }
                        }
                      }
                    }
                  }
                }
              }
            }
          }
        }
      }
      hull () {
        translate ([0, 0, 13]) {
          rotate (a=14.999999999999998, v=[0, 1, 0]) {
            translate ([28.8, 0, 0]) {
              translate ([0, 0, 0]) {
                translate ([0, 0, 239.07818057271746]) {
                  rotate (a=5.0, v=[0, 1, 0]) {
                    translate ([0, 0, -239.07818057271746]) {
                      translate ([0, 0, 85.26861330108649]) {
                        rotate (a=-29.999999999999996, v=[1, 0, 0]) {
                          translate ([0, 0, -85.26861330108649]) {
                            translate ([8.649999999999999, 8.649999999999999, 0]) {
                              translate ([0, 0, 2.25]) {
                                cube ([0.1, 0.1, 3.5], center=true);
                              }
                            }
                          }
                        }
                      }
                    }
                  }
                }
              }
            }
          }
        }
        translate ([0, 0, 13]) {
          rotate (a=14.999999999999998, v=[0, 1, 0]) {
            translate ([28.8, 0, 0]) {
              translate ([0, 2.82, -3.0]) {
                translate ([0, 0, 239.07818057271746]) {
                  rotate (a=0.0, v=[0, 1, 0]) {
                    translate ([0, 0, -239.07818057271746]) {
                      translate ([0, 0, 85.26861330108649]) {
                        rotate (a=-29.999999999999996, v=[1, 0, 0]) {
                          translate ([0, 0, -85.26861330108649]) {
                            translate ([-8.649999999999999, -8.649999999999999, 0]) {
                              translate ([0, 0, 2.25]) {
                                cube ([0.1, 0.1, 3.5], center=true);
                              }
                            }
                          }
                        }
                      }
                    }
                  }
                }
              }
            }
          }
        }
        translate ([0, 0, 13]) {
          rotate (a=14.999999999999998, v=[0, 1, 0]) {
            translate ([28.8, 0, 0]) {
              translate ([0, 0, 0]) {
                translate ([0, 0, 239.07818057271746]) {
                  rotate (a=5.0, v=[0, 1, 0]) {
                    translate ([0, 0, -239.07818057271746]) {
                      translate ([0, 0, 85.26861330108649]) {
                        rotate (a=-29.999999999999996, v=[1, 0, 0]) {
                          translate ([0, 0, -85.26861330108649]) {
                            translate ([8.649999999999999, -8.649999999999999, 0]) {
                              translate ([0, 0, 2.25]) {
                                cube ([0.1, 0.1, 3.5], center=true);
                              }
                            }
                          }
                        }
                      }
                    }
                  }
                }
              }
            }
          }
        }
      }
    }
    union () {
      hull () {
        translate ([0, 0, 13]) {
          rotate (a=14.999999999999998, v=[0, 1, 0]) {
            translate ([0, 0, 0]) {
              translate ([0, 0, 0]) {
                translate ([0, 0, 239.07818057271746]) {
                  rotate (a=-5.0, v=[0, 1, 0]) {
                    translate ([0, 0, -239.07818057271746]) {
                      translate ([0, 0, 85.26861330108649]) {
                        rotate (a=29.999999999999996, v=[1, 0, 0]) {
                          translate ([0, 0, -85.26861330108649]) {
                            translate ([-8.649999999999999, 8.649999999999999, 0]) {
                              translate ([0, 0, 2.25]) {
                                cube ([0.1, 0.1, 3.5], center=true);
                              }
                            }
                          }
                        }
                      }
                    }
                  }
                }
              }
            }
          }
        }
        translate ([0, 0, 13]) {
          rotate (a=14.999999999999998, v=[0, 1, 0]) {
            translate ([0, 0, 0]) {
              translate ([0, 2.82, -3.0]) {
                translate ([0, 0, 239.07818057271746]) {
                  rotate (a=0.0, v=[0, 1, 0]) {
                    translate ([0, 0, -239.07818057271746]) {
                      translate ([0, 0, 85.26861330108649]) {
                        rotate (a=29.999999999999996, v=[1, 0, 0]) {
                          translate ([0, 0, -85.26861330108649]) {
                            translate ([8.649999999999999, 8.649999999999999, 0]) {
                              translate ([0, 0, 2.25]) {
                                cube ([0.1, 0.1, 3.5], center=true);
                              }
                            }
                          }
                        }
                      }
                    }
                  }
                }
              }
            }
          }
        }
        translate ([0, 0, 13]) {
          rotate (a=14.999999999999998, v=[0, 1, 0]) {
            translate ([0, 0, 0]) {
              translate ([0, 0, 0]) {
                translate ([0, 0, 239.07818057271746]) {
                  rotate (a=-5.0, v=[0, 1, 0]) {
                    translate ([0, 0, -239.07818057271746]) {
                      translate ([0, 0, 85.26861330108649]) {
                        rotate (a=29.999999999999996, v=[1, 0, 0]) {
                          translate ([0, 0, -85.26861330108649]) {
                            translate ([-8.649999999999999, -8.649999999999999, 0]) {
                              translate ([0, 0, 2.25]) {
                                cube ([0.1, 0.1, 3.5], center=true);
                              }
                            }
                          }
                        }
                      }
                    }
                  }
                }
              }
            }
          }
        }
      }
      hull () {
        translate ([0, 0, 13]) {
          rotate (a=14.999999999999998, v=[0, 1, 0]) {
            translate ([0, 0, 0]) {
              translate ([0, 2.82, -3.0]) {
                translate ([0, 0, 239.07818057271746]) {
                  rotate (a=0.0, v=[0, 1, 0]) {
                    translate ([0, 0, -239.07818057271746]) {
                      translate ([0, 0, 85.26861330108649]) {
                        rotate (a=29.999999999999996, v=[1, 0, 0]) {
                          translate ([0, 0, -85.26861330108649]) {
                            translate ([8.649999999999999, 8.649999999999999, 0]) {
                              translate ([0, 0, 2.25]) {
                                cube ([0.1, 0.1, 3.5], center=true);
                              }
                            }
                          }
                        }
                      }
                    }
                  }
                }
              }
            }
          }
        }
        translate ([0, 0, 13]) {
          rotate (a=14.999999999999998, v=[0, 1, 0]) {
            translate ([0, 0, 0]) {
              translate ([0, 0, 0]) {
                translate ([0, 0, 239.07818057271746]) {
                  rotate (a=-5.0, v=[0, 1, 0]) {
                    translate ([0, 0, -239.07818057271746]) {
                      translate ([0, 0, 85.26861330108649]) {
                        rotate (a=29.999999999999996, v=[1, 0, 0]) {
                          translate ([0, 0, -85.26861330108649]) {
                            translate ([-8.649999999999999, -8.649999999999999, 0]) {
                              translate ([0, 0, 2.25]) {
                                cube ([0.1, 0.1, 3.5], center=true);
                              }
                            }
                          }
                        }
                      }
                    }
                  }
                }
              }
            }
          }
        }
        translate ([0, 0, 13]) {
          rotate (a=14.999999999999998, v=[0, 1, 0]) {
            translate ([0, 0, 0]) {
              translate ([0, 2.82, -3.0]) {
                translate ([0, 0, 239.07818057271746]) {
                  rotate (a=0.0, v=[0, 1, 0]) {
                    translate ([0, 0, -239.07818057271746]) {
                      translate ([0, 0, 85.26861330108649]) {
                        rotate (a=29.999999999999996, v=[1, 0, 0]) {
                          translate ([0, 0, -85.26861330108649]) {
                            translate ([8.649999999999999, -8.649999999999999, 0]) {
                              translate ([0, 0, 2.25]) {
                                cube ([0.1, 0.1, 3.5], center=true);
                              }
                            }
                          }
                        }
                      }
                    }
                  }
                }
              }
            }
          }
        }
      }
    }
    union () {
      hull () {
        translate ([0, 0, 13]) {
          rotate (a=14.999999999999998, v=[0, 1, 0]) {
            translate ([7.2, 0, 0]) {
              translate ([0, 0, 0]) {
                translate ([0, 0, 239.07818057271746]) {
                  rotate (a=-5.0, v=[0, 1, 0]) {
                    translate ([0, 0, -239.07818057271746]) {
                      translate ([0, 0, 85.26861330108649]) {
                        rotate (a=14.999999999999998, v=[1, 0, 0]) {
                          translate ([0, 0, -85.26861330108649]) {
                            translate ([-8.649999999999999, 8.649999999999999, 0]) {
                              translate ([0, 0, 2.25]) {
                                cube ([0.1, 0.1, 3.5], center=true);
                              }
                            }
                          }
                        }
                      }
                    }
                  }
                }
              }
            }
          }
        }
        translate ([0, 0, 13]) {
          rotate (a=14.999999999999998, v=[0, 1, 0]) {
            translate ([7.2, 0, 0]) {
              translate ([0, 2.82, -3.0]) {
                translate ([0, 0, 239.07818057271746]) {
                  rotate (a=0.0, v=[0, 1, 0]) {
                    translate ([0, 0, -239.07818057271746]) {
                      translate ([0, 0, 85.26861330108649]) {
                        rotate (a=14.999999999999998, v=[1, 0, 0]) {
                          translate ([0, 0, -85.26861330108649]) {
                            translate ([8.649999999999999, 8.649999999999999, 0]) {
                              translate ([0, 0, 2.25]) {
                                cube ([0.1, 0.1, 3.5], center=true);
                              }
                            }
                          }
                        }
                      }
                    }
                  }
                }
              }
            }
          }
        }
        translate ([0, 0, 13]) {
          rotate (a=14.999999999999998, v=[0, 1, 0]) {
            translate ([7.2, 0, 0]) {
              translate ([0, 0, 0]) {
                translate ([0, 0, 239.07818057271746]) {
                  rotate (a=-5.0, v=[0, 1, 0]) {
                    translate ([0, 0, -239.07818057271746]) {
                      translate ([0, 0, 85.26861330108649]) {
                        rotate (a=14.999999999999998, v=[1, 0, 0]) {
                          translate ([0, 0, -85.26861330108649]) {
                            translate ([-8.649999999999999, -8.649999999999999, 0]) {
                              translate ([0, 0, 2.25]) {
                                cube ([0.1, 0.1, 3.5], center=true);
                              }
                            }
                          }
                        }
                      }
                    }
                  }
                }
              }
            }
          }
        }
      }
      hull () {
        translate ([0, 0, 13]) {
          rotate (a=14.999999999999998, v=[0, 1, 0]) {
            translate ([7.2, 0, 0]) {
              translate ([0, 2.82, -3.0]) {
                translate ([0, 0, 239.07818057271746]) {
                  rotate (a=0.0, v=[0, 1, 0]) {
                    translate ([0, 0, -239.07818057271746]) {
                      translate ([0, 0, 85.26861330108649]) {
                        rotate (a=14.999999999999998, v=[1, 0, 0]) {
                          translate ([0, 0, -85.26861330108649]) {
                            translate ([8.649999999999999, 8.649999999999999, 0]) {
                              translate ([0, 0, 2.25]) {
                                cube ([0.1, 0.1, 3.5], center=true);
                              }
                            }
                          }
                        }
                      }
                    }
                  }
                }
              }
            }
          }
        }
        translate ([0, 0, 13]) {
          rotate (a=14.999999999999998, v=[0, 1, 0]) {
            translate ([7.2, 0, 0]) {
              translate ([0, 0, 0]) {
                translate ([0, 0, 239.07818057271746]) {
                  rotate (a=-5.0, v=[0, 1, 0]) {
                    translate ([0, 0, -239.07818057271746]) {
                      translate ([0, 0, 85.26861330108649]) {
                        rotate (a=14.999999999999998, v=[1, 0, 0]) {
                          translate ([0, 0, -85.26861330108649]) {
                            translate ([-8.649999999999999, -8.649999999999999, 0]) {
                              translate ([0, 0, 2.25]) {
                                cube ([0.1, 0.1, 3.5], center=true);
                              }
                            }
                          }
                        }
                      }
                    }
                  }
                }
              }
            }
          }
        }
        translate ([0, 0, 13]) {
          rotate (a=14.999999999999998, v=[0, 1, 0]) {
            translate ([7.2, 0, 0]) {
              translate ([0, 2.82, -3.0]) {
                translate ([0, 0, 239.07818057271746]) {
                  rotate (a=0.0, v=[0, 1, 0]) {
                    translate ([0, 0, -239.07818057271746]) {
                      translate ([0, 0, 85.26861330108649]) {
                        rotate (a=14.999999999999998, v=[1, 0, 0]) {
                          translate ([0, 0, -85.26861330108649]) {
                            translate ([8.649999999999999, -8.649999999999999, 0]) {
                              translate ([0, 0, 2.25]) {
                                cube ([0.1, 0.1, 3.5], center=true);
                              }
                            }
                          }
                        }
                      }
                    }
                  }
                }
              }
            }
          }
        }
      }
    }
    union () {
      hull () {
        translate ([0, 0, 13]) {
          rotate (a=14.999999999999998, v=[0, 1, 0]) {
            translate ([14.4, 0, 0]) {
              translate ([0, 0, 0]) {
                translate ([0, 0, 239.07818057271746]) {
                  rotate (a=-5.0, v=[0, 1, 0]) {
                    translate ([0, 0, -239.07818057271746]) {
                      translate ([0, 0, 85.26861330108649]) {
                        rotate (a=0.0, v=[1, 0, 0]) {
                          translate ([0, 0, -85.26861330108649]) {
                            translate ([-8.649999999999999, 8.649999999999999, 0]) {
                              translate ([0, 0, 2.25]) {
                                cube ([0.1, 0.1, 3.5], center=true);
                              }
                            }
                          }
                        }
                      }
                    }
                  }
                }
              }
            }
          }
        }
        translate ([0, 0, 13]) {
          rotate (a=14.999999999999998, v=[0, 1, 0]) {
            translate ([14.4, 0, 0]) {
              translate ([0, 2.82, -3.0]) {
                translate ([0, 0, 239.07818057271746]) {
                  rotate (a=0.0, v=[0, 1, 0]) {
                    translate ([0, 0, -239.07818057271746]) {
                      translate ([0, 0, 85.26861330108649]) {
                        rotate (a=0.0, v=[1, 0, 0]) {
                          translate ([0, 0, -85.26861330108649]) {
                            translate ([8.649999999999999, 8.649999999999999, 0]) {
                              translate ([0, 0, 2.25]) {
                                cube ([0.1, 0.1, 3.5], center=true);
                              }
                            }
                          }
                        }
                      }
                    }
                  }
                }
              }
            }
          }
        }
        translate ([0, 0, 13]) {
          rotate (a=14.999999999999998, v=[0, 1, 0]) {
            translate ([14.4, 0, 0]) {
              translate ([0, 0, 0]) {
                translate ([0, 0, 239.07818057271746]) {
                  rotate (a=-5.0, v=[0, 1, 0]) {
                    translate ([0, 0, -239.07818057271746]) {
                      translate ([0, 0, 85.26861330108649]) {
                        rotate (a=0.0, v=[1, 0, 0]) {
                          translate ([0, 0, -85.26861330108649]) {
                            translate ([-8.649999999999999, -8.649999999999999, 0]) {
                              translate ([0, 0, 2.25]) {
                                cube ([0.1, 0.1, 3.5], center=true);
                              }
                            }
                          }
                        }
                      }
                    }
                  }
                }
              }
            }
          }
        }
      }
      hull () {
        translate ([0, 0, 13]) {
          rotate (a=14.999999999999998, v=[0, 1, 0]) {
            translate ([14.4, 0, 0]) {
              translate ([0, 2.82, -3.0]) {
                translate ([0, 0, 239.07818057271746]) {
                  rotate (a=0.0, v=[0, 1, 0]) {
                    translate ([0, 0, -239.07818057271746]) {
                      translate ([0, 0, 85.26861330108649]) {
                        rotate (a=0.0, v=[1, 0, 0]) {
                          translate ([0, 0, -85.26861330108649]) {
                            translate ([8.649999999999999, 8.649999999999999, 0]) {
                              translate ([0, 0, 2.25]) {
                                cube ([0.1, 0.1, 3.5], center=true);
                              }
                            }
                          }
                        }
                      }
                    }
                  }
                }
              }
            }
          }
        }
        translate ([0, 0, 13]) {
          rotate (a=14.999999999999998, v=[0, 1, 0]) {
            translate ([14.4, 0, 0]) {
              translate ([0, 0, 0]) {
                translate ([0, 0, 239.07818057271746]) {
                  rotate (a=-5.0, v=[0, 1, 0]) {
                    translate ([0, 0, -239.07818057271746]) {
                      translate ([0, 0, 85.26861330108649]) {
                        rotate (a=0.0, v=[1, 0, 0]) {
                          translate ([0, 0, -85.26861330108649]) {
                            translate ([-8.649999999999999, -8.649999999999999, 0]) {
                              translate ([0, 0, 2.25]) {
                                cube ([0.1, 0.1, 3.5], center=true);
                              }
                            }
                          }
                        }
                      }
                    }
                  }
                }
              }
            }
          }
        }
        translate ([0, 0, 13]) {
          rotate (a=14.999999999999998, v=[0, 1, 0]) {
            translate ([14.4, 0, 0]) {
              translate ([0, 2.82, -3.0]) {
                translate ([0, 0, 239.07818057271746]) {
                  rotate (a=0.0, v=[0, 1, 0]) {
                    translate ([0, 0, -239.07818057271746]) {
                      translate ([0, 0, 85.26861330108649]) {
                        rotate (a=0.0, v=[1, 0, 0]) {
                          translate ([0, 0, -85.26861330108649]) {
                            translate ([8.649999999999999, -8.649999999999999, 0]) {
                              translate ([0, 0, 2.25]) {
                                cube ([0.1, 0.1, 3.5], center=true);
                              }
                            }
                          }
                        }
                      }
                    }
                  }
                }
              }
            }
          }
        }
      }
    }
    union () {
      hull () {
        translate ([0, 0, 13]) {
          rotate (a=14.999999999999998, v=[0, 1, 0]) {
            translate ([21.6, 0, 0]) {
              translate ([0, 0, 0]) {
                translate ([0, 0, 239.07818057271746]) {
                  rotate (a=-5.0, v=[0, 1, 0]) {
                    translate ([0, 0, -239.07818057271746]) {
                      translate ([0, 0, 85.26861330108649]) {
                        rotate (a=-14.999999999999998, v=[1, 0, 0]) {
                          translate ([0, 0, -85.26861330108649]) {
                            translate ([-8.649999999999999, 8.649999999999999, 0]) {
                              translate ([0, 0, 2.25]) {
                                cube ([0.1, 0.1, 3.5], center=true);
                              }
                            }
                          }
                        }
                      }
                    }
                  }
                }
              }
            }
          }
        }
        translate ([0, 0, 13]) {
          rotate (a=14.999999999999998, v=[0, 1, 0]) {
            translate ([21.6, 0, 0]) {
              translate ([0, 2.82, -3.0]) {
                translate ([0, 0, 239.07818057271746]) {
                  rotate (a=0.0, v=[0, 1, 0]) {
                    translate ([0, 0, -239.07818057271746]) {
                      translate ([0, 0, 85.26861330108649]) {
                        rotate (a=-14.999999999999998, v=[1, 0, 0]) {
                          translate ([0, 0, -85.26861330108649]) {
                            translate ([8.649999999999999, 8.649999999999999, 0]) {
                              translate ([0, 0, 2.25]) {
                                cube ([0.1, 0.1, 3.5], center=true);
                              }
                            }
                          }
                        }
                      }
                    }
                  }
                }
              }
            }
          }
        }
        translate ([0, 0, 13]) {
          rotate (a=14.999999999999998, v=[0, 1, 0]) {
            translate ([21.6, 0, 0]) {
              translate ([0, 0, 0]) {
                translate ([0, 0, 239.07818057271746]) {
                  rotate (a=-5.0, v=[0, 1, 0]) {
                    translate ([0, 0, -239.07818057271746]) {
                      translate ([0, 0, 85.26861330108649]) {
                        rotate (a=-14.999999999999998, v=[1, 0, 0]) {
                          translate ([0, 0, -85.26861330108649]) {
                            translate ([-8.649999999999999, -8.649999999999999, 0]) {
                              translate ([0, 0, 2.25]) {
                                cube ([0.1, 0.1, 3.5], center=true);
                              }
                            }
                          }
                        }
                      }
                    }
                  }
                }
              }
            }
          }
        }
      }
      hull () {
        translate ([0, 0, 13]) {
          rotate (a=14.999999999999998, v=[0, 1, 0]) {
            translate ([21.6, 0, 0]) {
              translate ([0, 2.82, -3.0]) {
                translate ([0, 0, 239.07818057271746]) {
                  rotate (a=0.0, v=[0, 1, 0]) {
                    translate ([0, 0, -239.07818057271746]) {
                      translate ([0, 0, 85.26861330108649]) {
                        rotate (a=-14.999999999999998, v=[1, 0, 0]) {
                          translate ([0, 0, -85.26861330108649]) {
                            translate ([8.649999999999999, 8.649999999999999, 0]) {
                              translate ([0, 0, 2.25]) {
                                cube ([0.1, 0.1, 3.5], center=true);
                              }
                            }
                          }
                        }
                      }
                    }
                  }
                }
              }
            }
          }
        }
        translate ([0, 0, 13]) {
          rotate (a=14.999999999999998, v=[0, 1, 0]) {
            translate ([21.6, 0, 0]) {
              translate ([0, 0, 0]) {
                translate ([0, 0, 239.07818057271746]) {
                  rotate (a=-5.0, v=[0, 1, 0]) {
                    translate ([0, 0, -239.07818057271746]) {
                      translate ([0, 0, 85.26861330108649]) {
                        rotate (a=-14.999999999999998, v=[1, 0, 0]) {
                          translate ([0, 0, -85.26861330108649]) {
                            translate ([-8.649999999999999, -8.649999999999999, 0]) {
                              translate ([0, 0, 2.25]) {
                                cube ([0.1, 0.1, 3.5], center=true);
                              }
                            }
                          }
                        }
                      }
                    }
                  }
                }
              }
            }
          }
        }
        translate ([0, 0, 13]) {
          rotate (a=14.999999999999998, v=[0, 1, 0]) {
            translate ([21.6, 0, 0]) {
              translate ([0, 2.82, -3.0]) {
                translate ([0, 0, 239.07818057271746]) {
                  rotate (a=0.0, v=[0, 1, 0]) {
                    translate ([0, 0, -239.07818057271746]) {
                      translate ([0, 0, 85.26861330108649]) {
                        rotate (a=-14.999999999999998, v=[1, 0, 0]) {
                          translate ([0, 0, -85.26861330108649]) {
                            translate ([8.649999999999999, -8.649999999999999, 0]) {
                              translate ([0, 0, 2.25]) {
                                cube ([0.1, 0.1, 3.5], center=true);
                              }
                            }
                          }
                        }
                      }
                    }
                  }
                }
              }
            }
          }
        }
      }
    }
    union () {
      hull () {
        translate ([0, 0, 13]) {
          rotate (a=14.999999999999998, v=[0, 1, 0]) {
            translate ([28.8, 0, 0]) {
              translate ([0, 0, 0]) {
                translate ([0, 0, 239.07818057271746]) {
                  rotate (a=-5.0, v=[0, 1, 0]) {
                    translate ([0, 0, -239.07818057271746]) {
                      translate ([0, 0, 85.26861330108649]) {
                        rotate (a=-29.999999999999996, v=[1, 0, 0]) {
                          translate ([0, 0, -85.26861330108649]) {
                            translate ([-8.649999999999999, 8.649999999999999, 0]) {
                              translate ([0, 0, 2.25]) {
                                cube ([0.1, 0.1, 3.5], center=true);
                              }
                            }
                          }
                        }
                      }
                    }
                  }
                }
              }
            }
          }
        }
        translate ([0, 0, 13]) {
          rotate (a=14.999999999999998, v=[0, 1, 0]) {
            translate ([28.8, 0, 0]) {
              translate ([0, 2.82, -3.0]) {
                translate ([0, 0, 239.07818057271746]) {
                  rotate (a=0.0, v=[0, 1, 0]) {
                    translate ([0, 0, -239.07818057271746]) {
                      translate ([0, 0, 85.26861330108649]) {
                        rotate (a=-29.999999999999996, v=[1, 0, 0]) {
                          translate ([0, 0, -85.26861330108649]) {
                            translate ([8.649999999999999, 8.649999999999999, 0]) {
                              translate ([0, 0, 2.25]) {
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
